Tai-Min/Azure-Sphere-Home-Process-Controller/Controller/code/Azure_Controller/Azure_Controller/RealTimeCore/control.h

#pragma once

/**
* @brief Read inputs, perform selected control algorithm then write outputs. Also check state of peripheral boards.
*
* @param pParams unused.
*/
void CONTROL_controlTask(void* pParams);
